floodnet-nyc/flood-sensor/deployment/img/Behind the signs.jpg

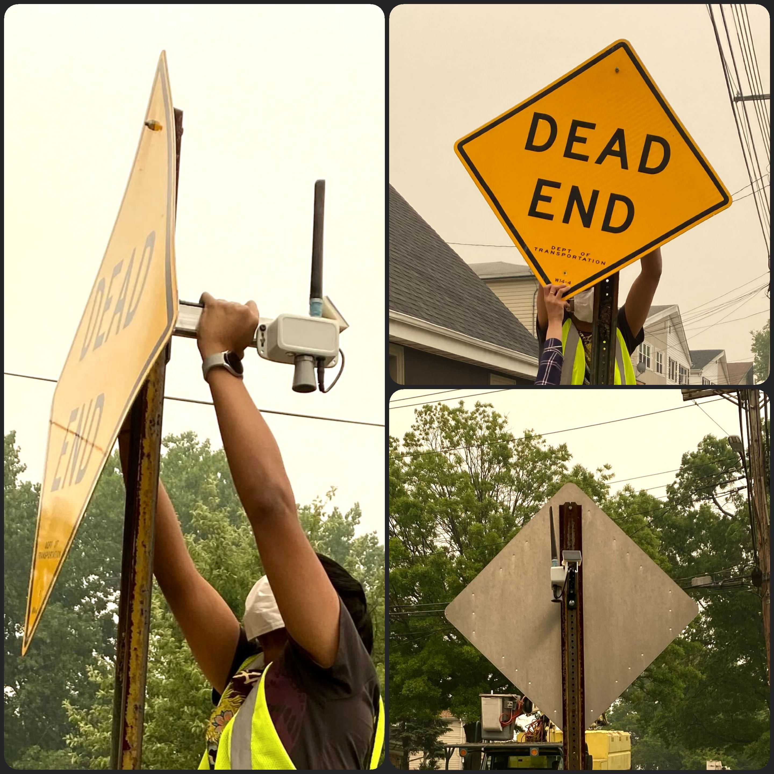
deployment/img/Behind the signs.jpg
