floodnet-nyc/flood-sensor/deployment/img/IMG_3310.jpg

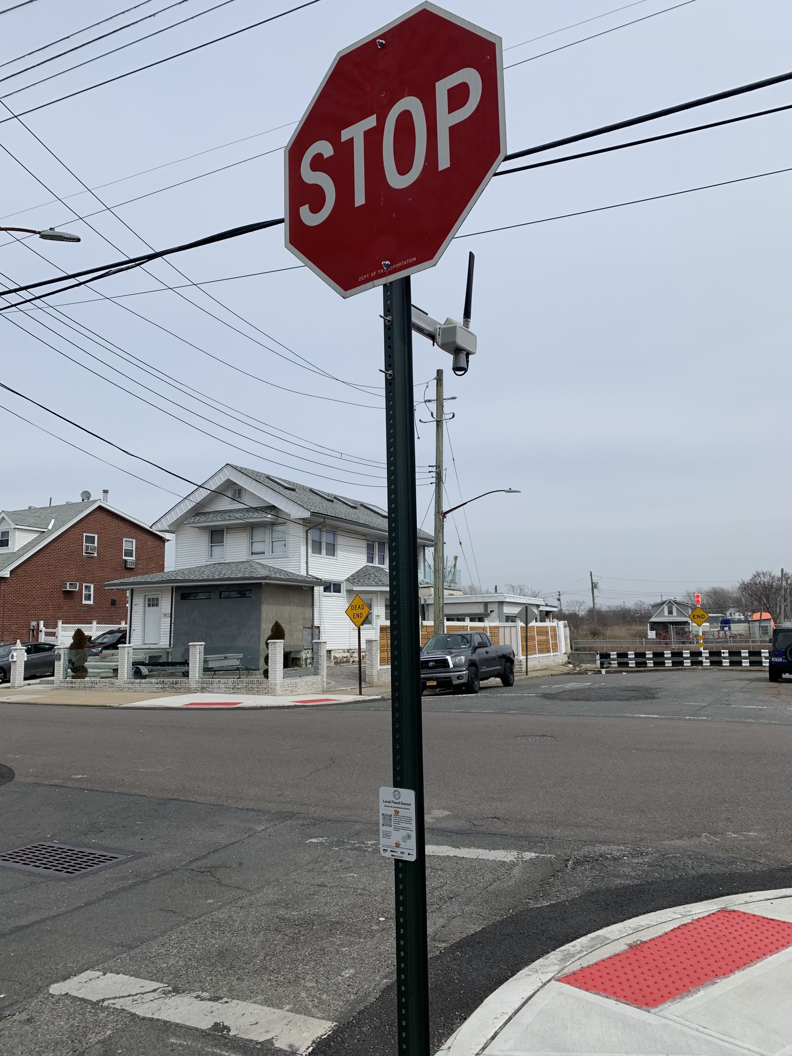
deployment/img/IMG_3310.jpg
