floodnet-nyc/flood-sensor/deployment/img/IMG_3319.jpg

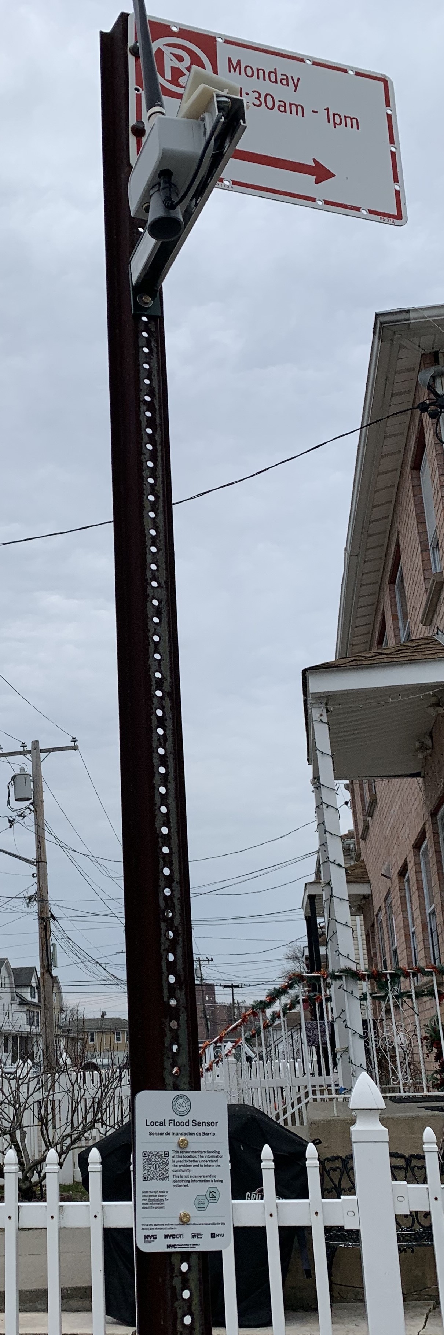
deployment/img/IMG_3319.jpg
