floodnet-nyc/flood-sensor/deployment/img/IMG_3345-1.jpg

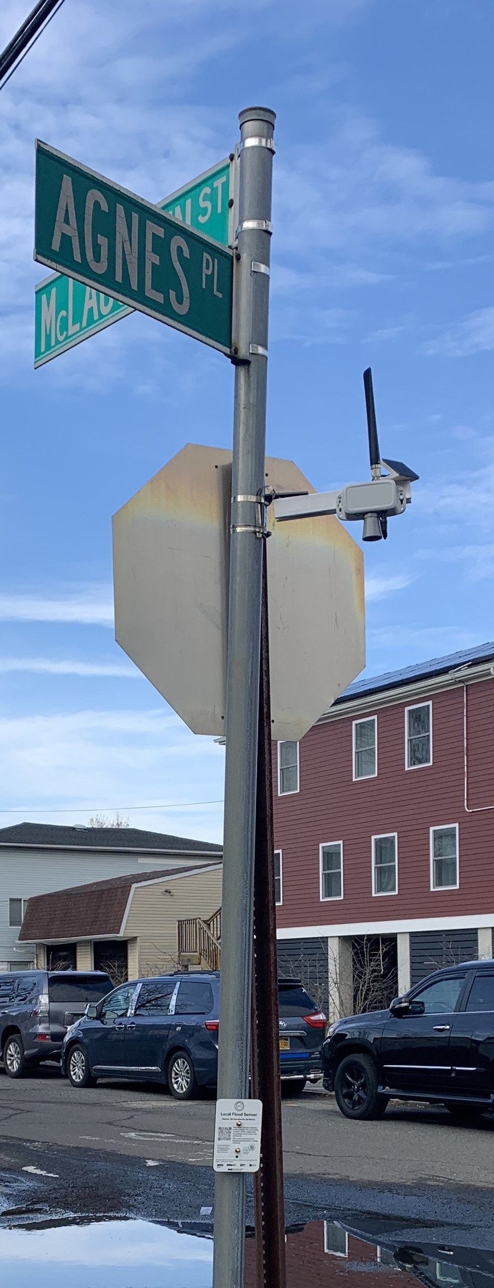
deployment/img/IMG_3345-1.jpg
