floodnet-nyc/flood-sensor/deployment/img/IMG_33191.jpg

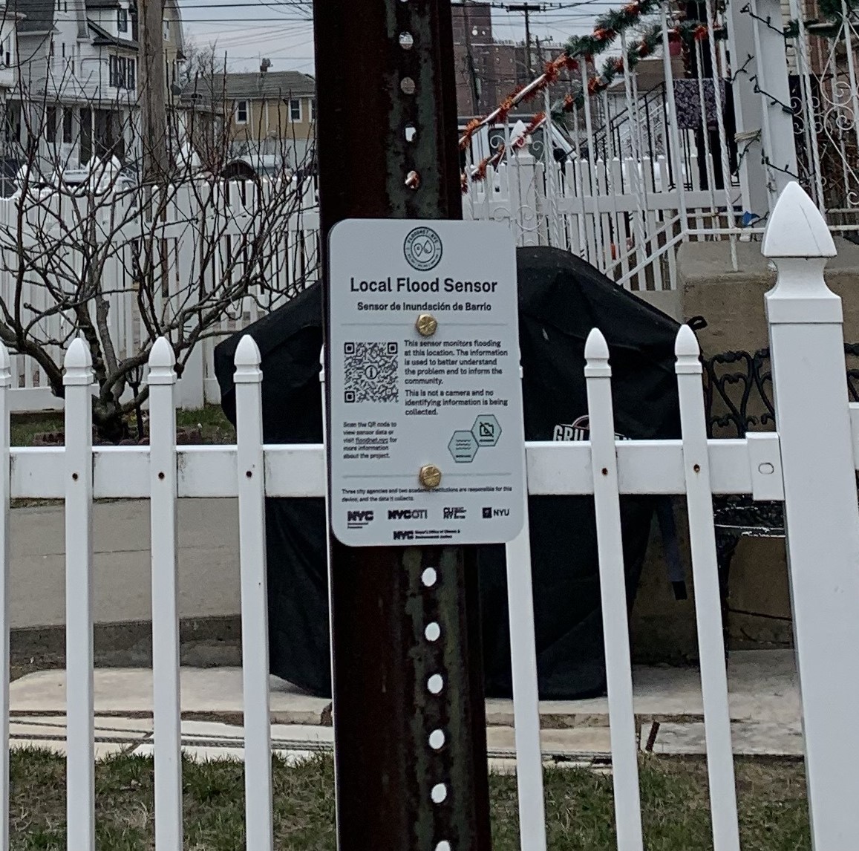
deployment/img/IMG_33191.jpg
