floodnet-nyc/flood-sensor/deployment/img/Sensor on Round pole.jpeg

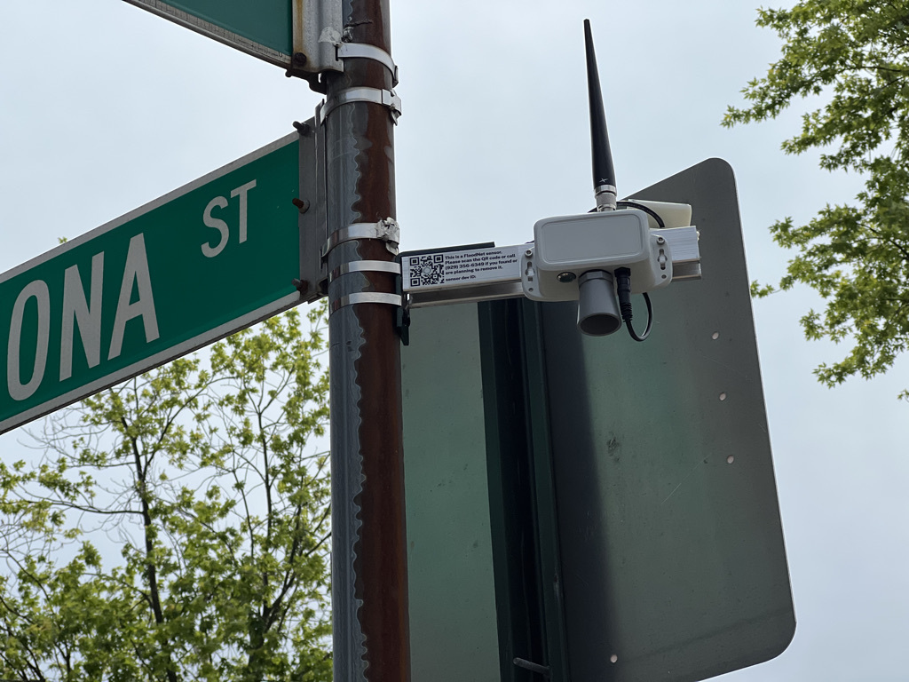
deployment/img/Sensor on Round pole.jpeg
