floodnet-nyc/flood-sensor/img/add-library.png

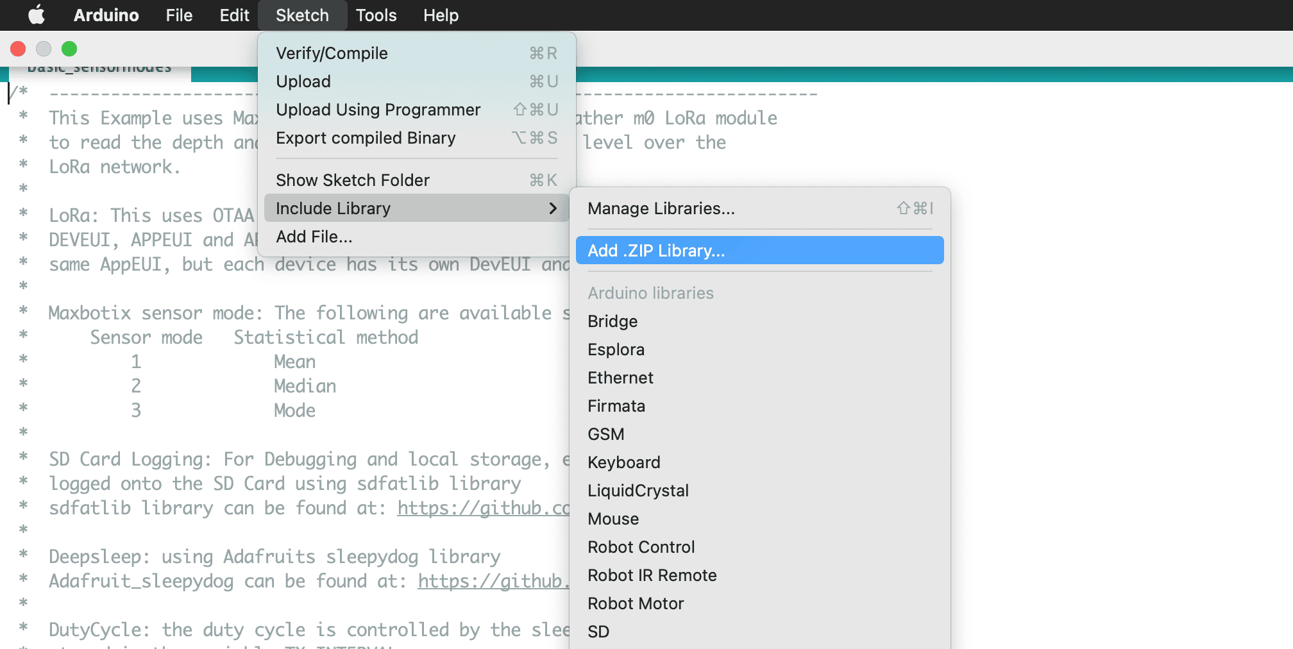
img/add-library.png
