floodnet-nyc/flood-sensor/img/deployment-render.png

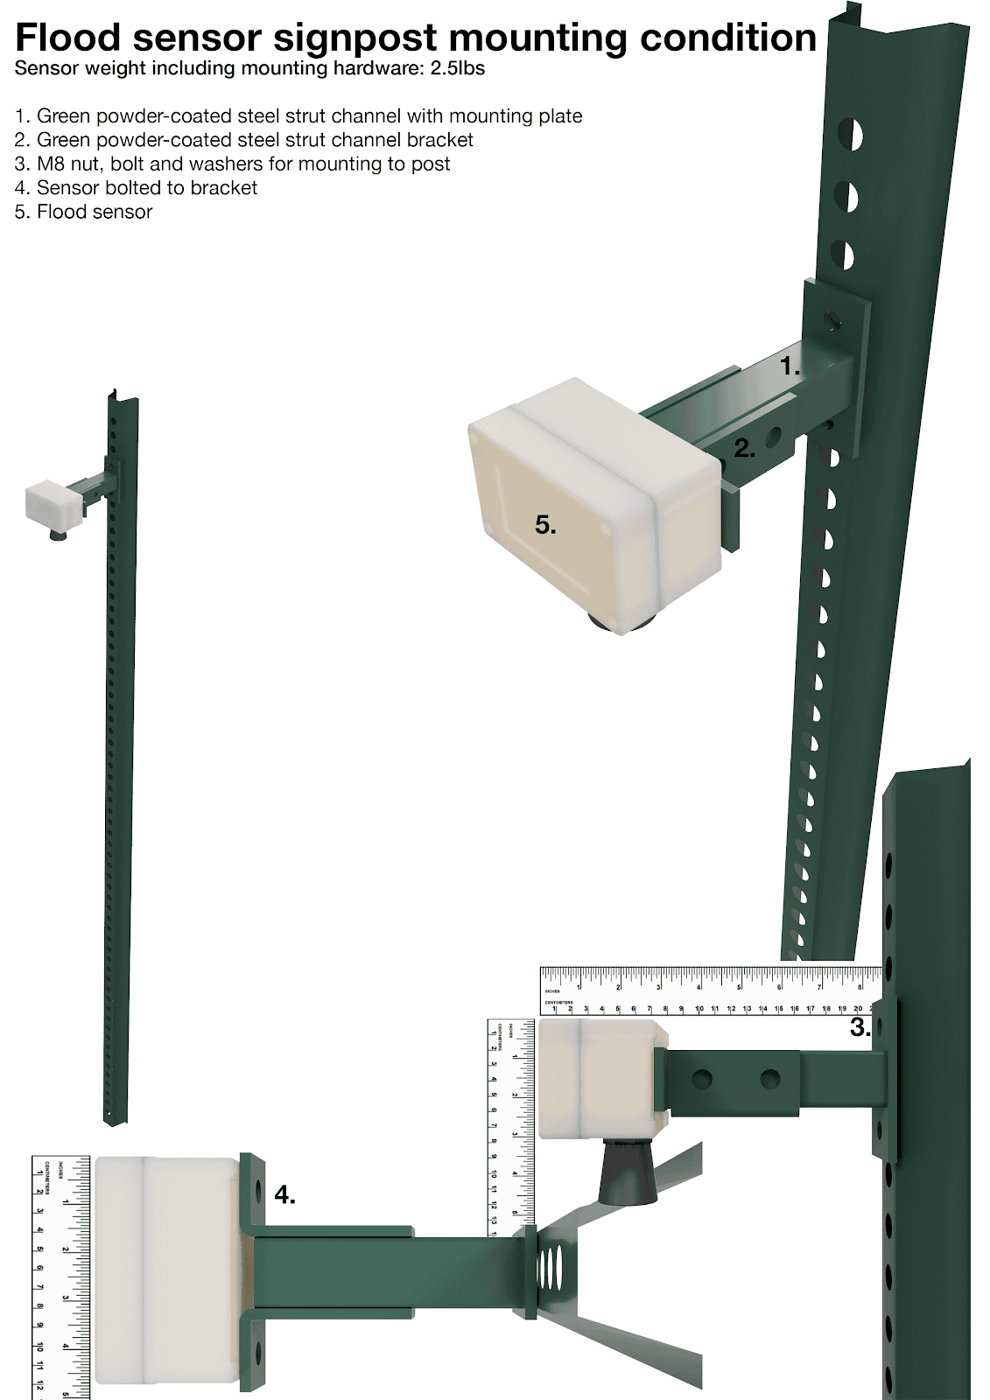
img/deployment-render.png
