floodnet-nyc/flood-sensor/img/design-data-comparison.png

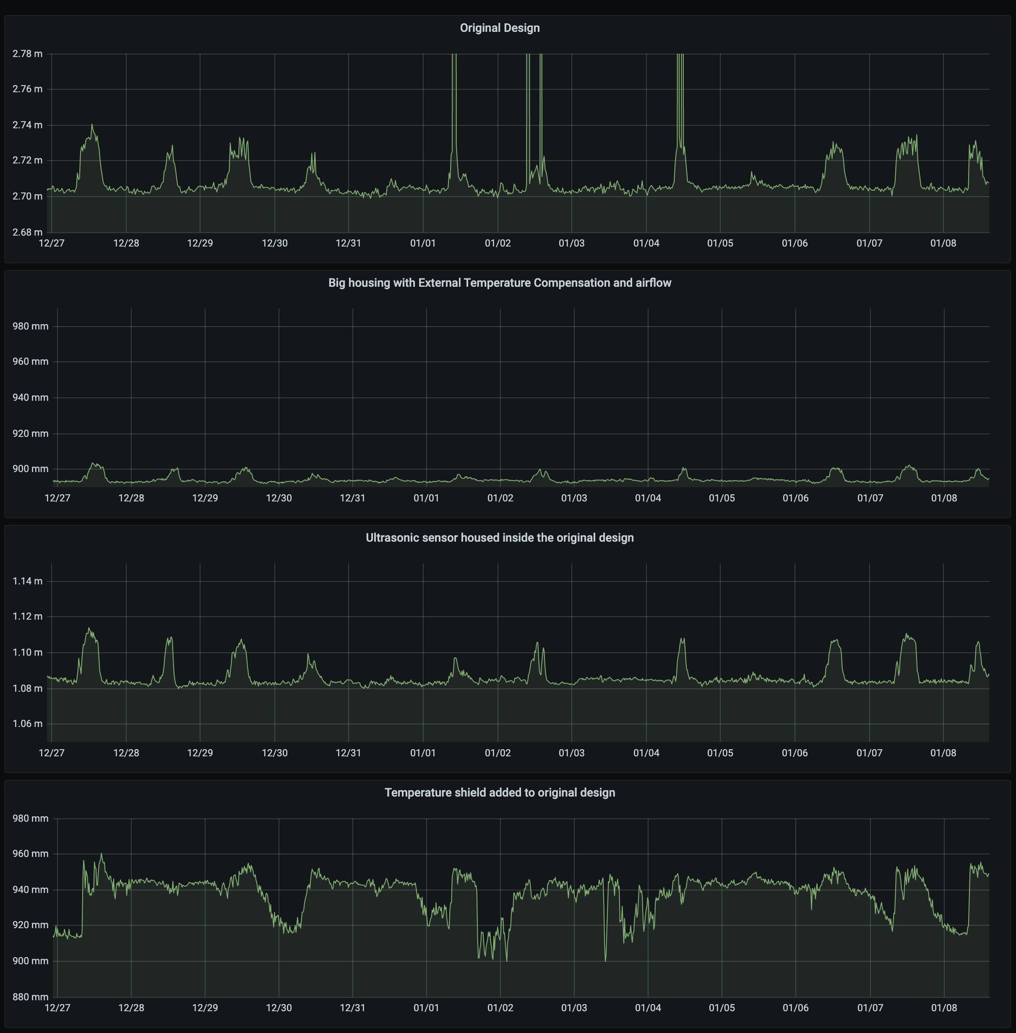
img/design-data-comparison.png
