floodnet-nyc/flood-sensor/img/fritzingcircuit.png

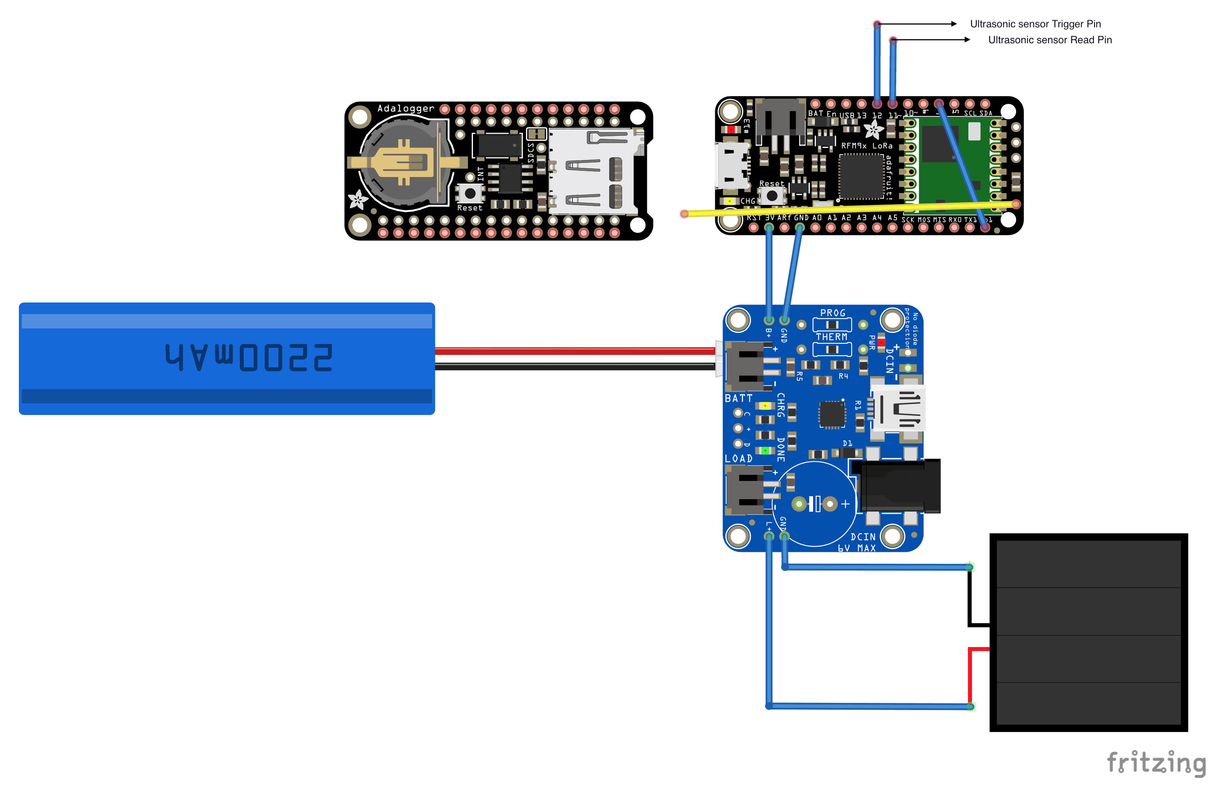
img/fritzingcircuit.png
