floodnet-nyc/flood-sensor/img/front-side-mount-sideview.png

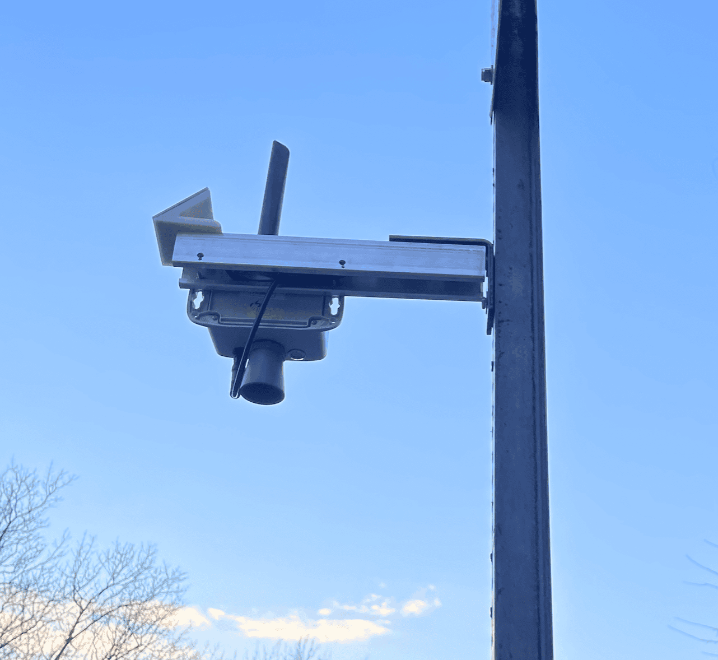
img/front-side-mount-sideview.png
