floodnet-nyc/flood-sensor/img/lora-timing.png

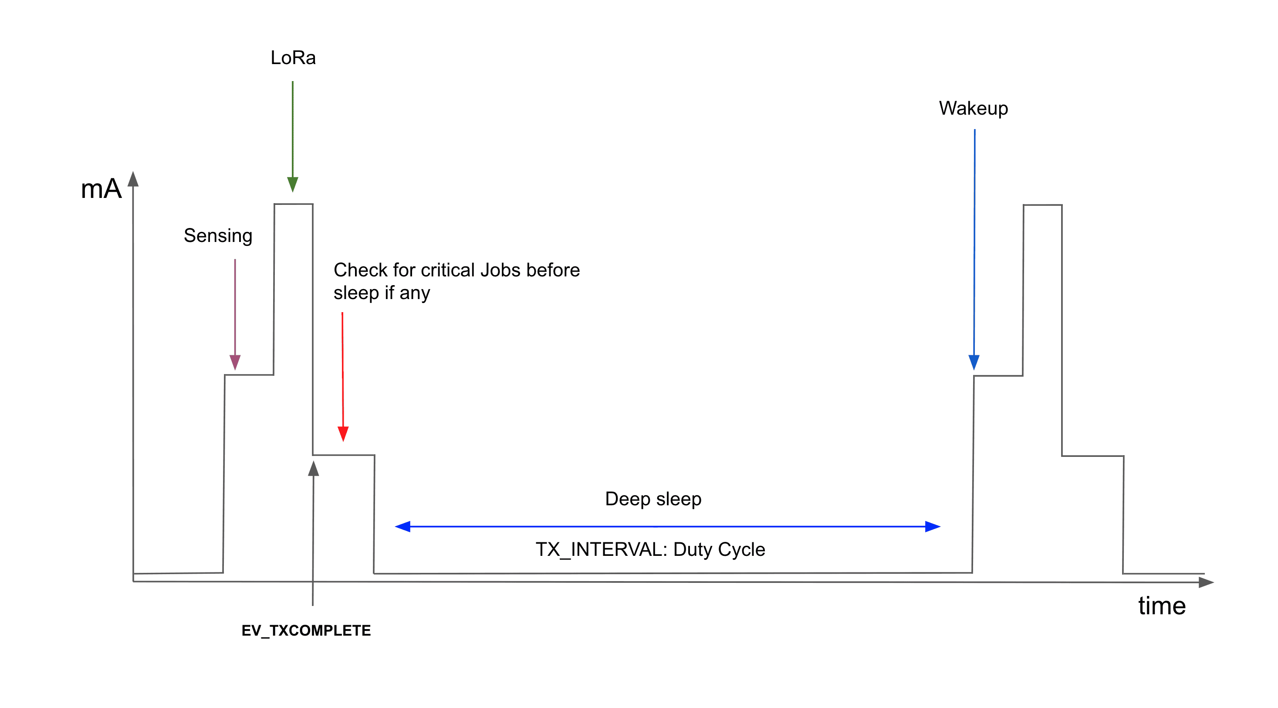
img/lora-timing.png
