floodnet-nyc/flood-sensor/img/low-power-profile.png

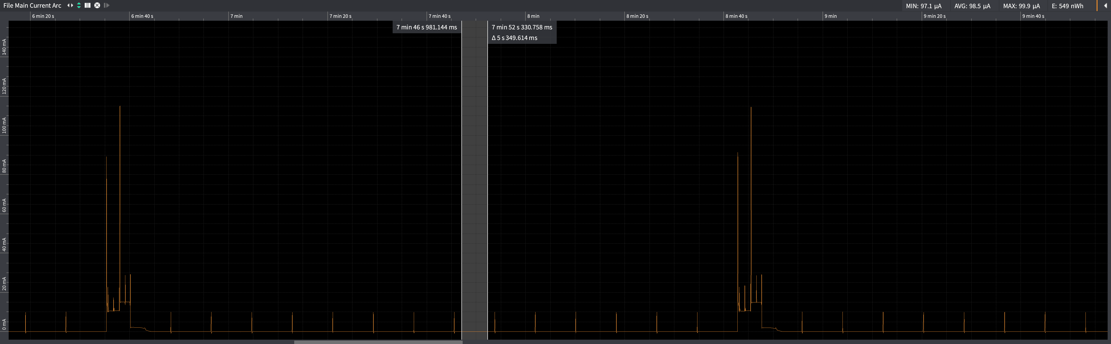
img/low-power-profile.png
