floodnet-nyc/flood-sensor/img/modes_cm.png

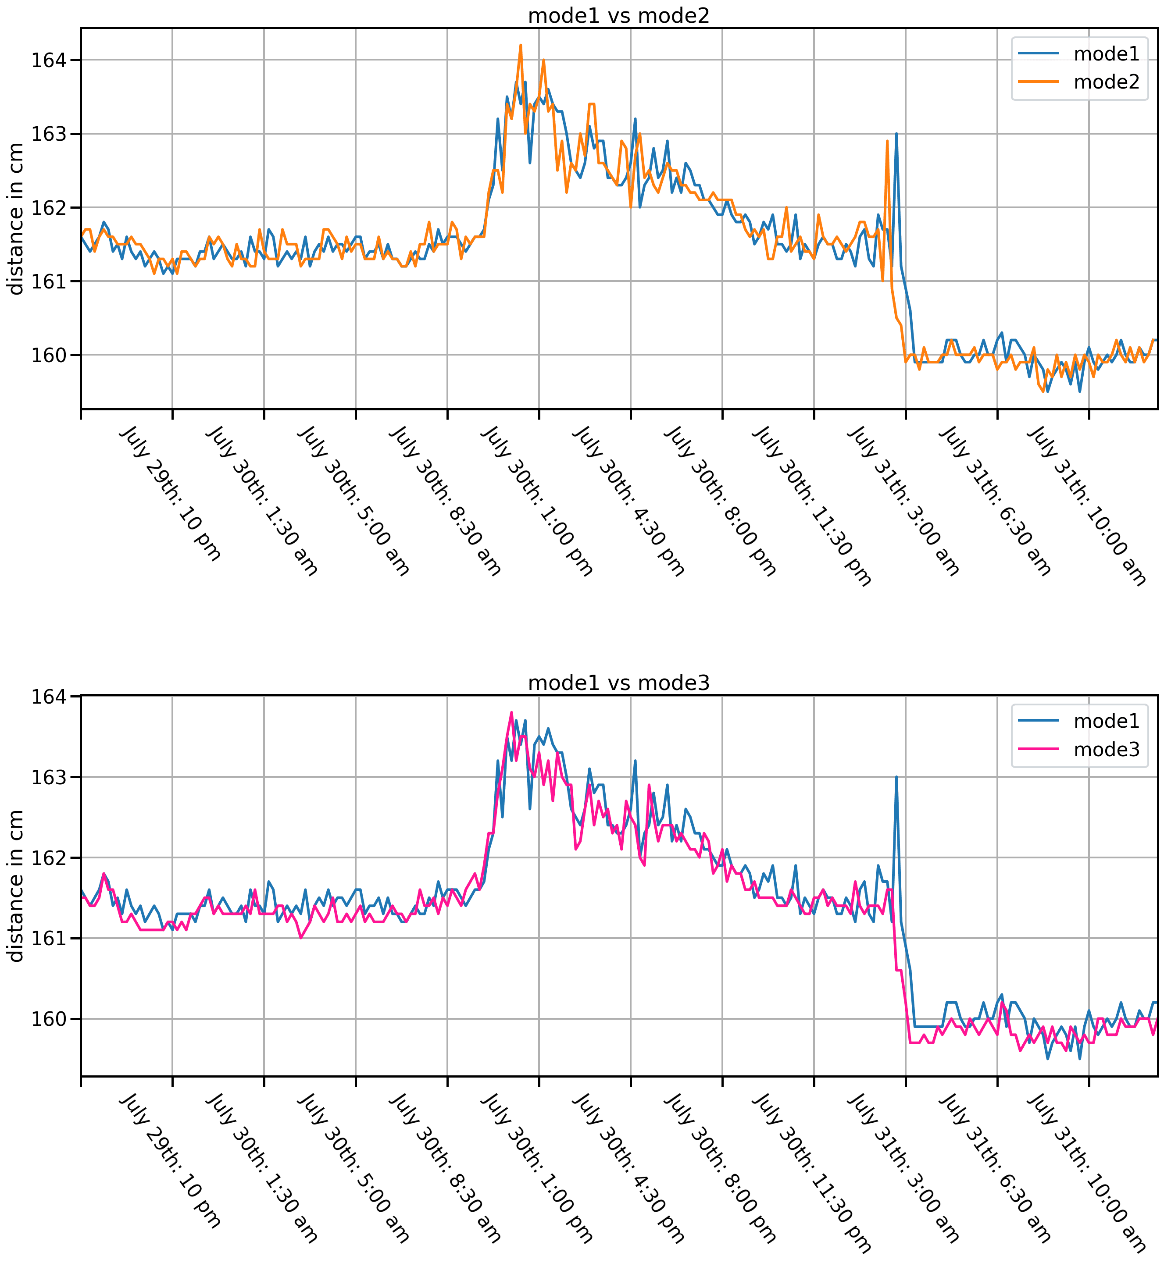
img/modes_cm.png
