floodnet-nyc/flood-sensor/img/mountedv2.jpg

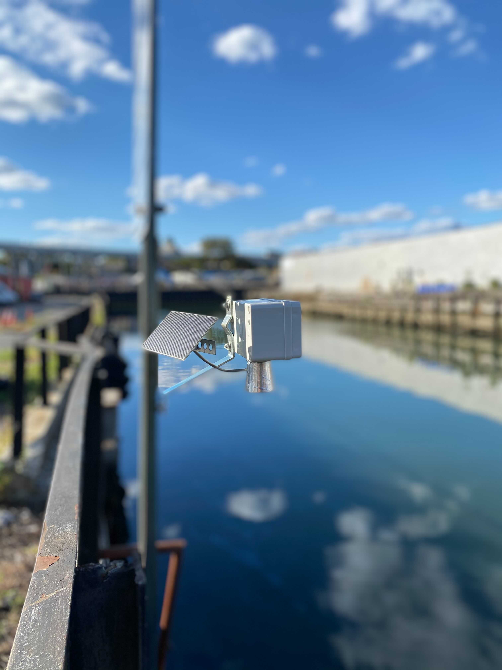
img/mountedv2.jpg
