floodnet-nyc/flood-sensor/img/mounting-seperate-solarboard.jpg

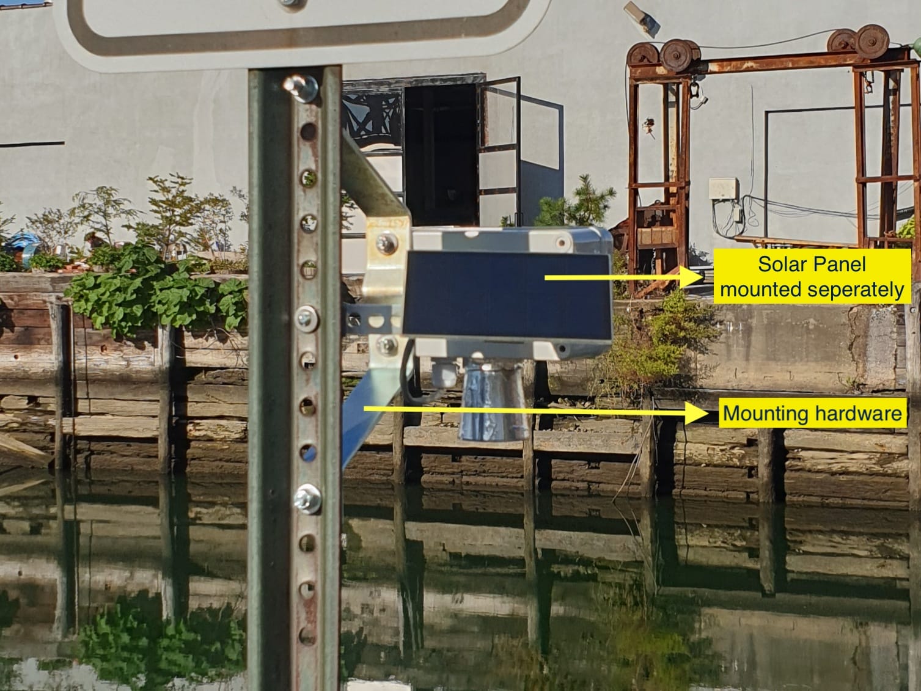
img/mounting-seperate-solarboard.jpg
