floodnet-nyc/flood-sensor/img/sensor-over-sidewalk.jpg

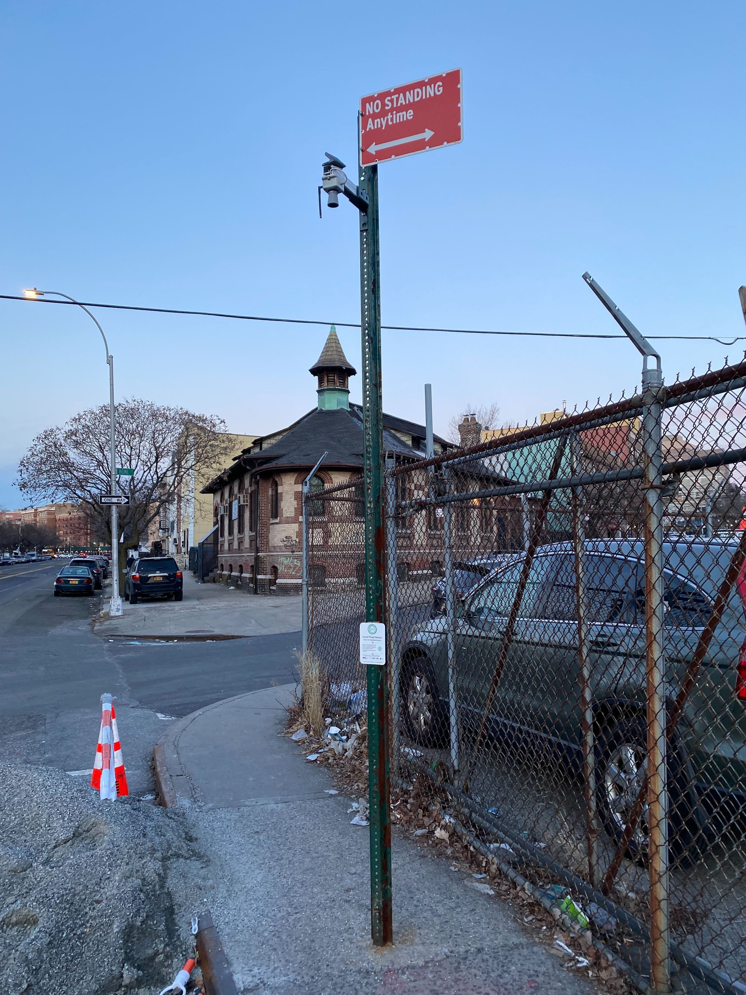
img/sensor-over-sidewalk.jpg
