floodnet-nyc/flood-sensor/img/sensor_states_flow_diagram.png

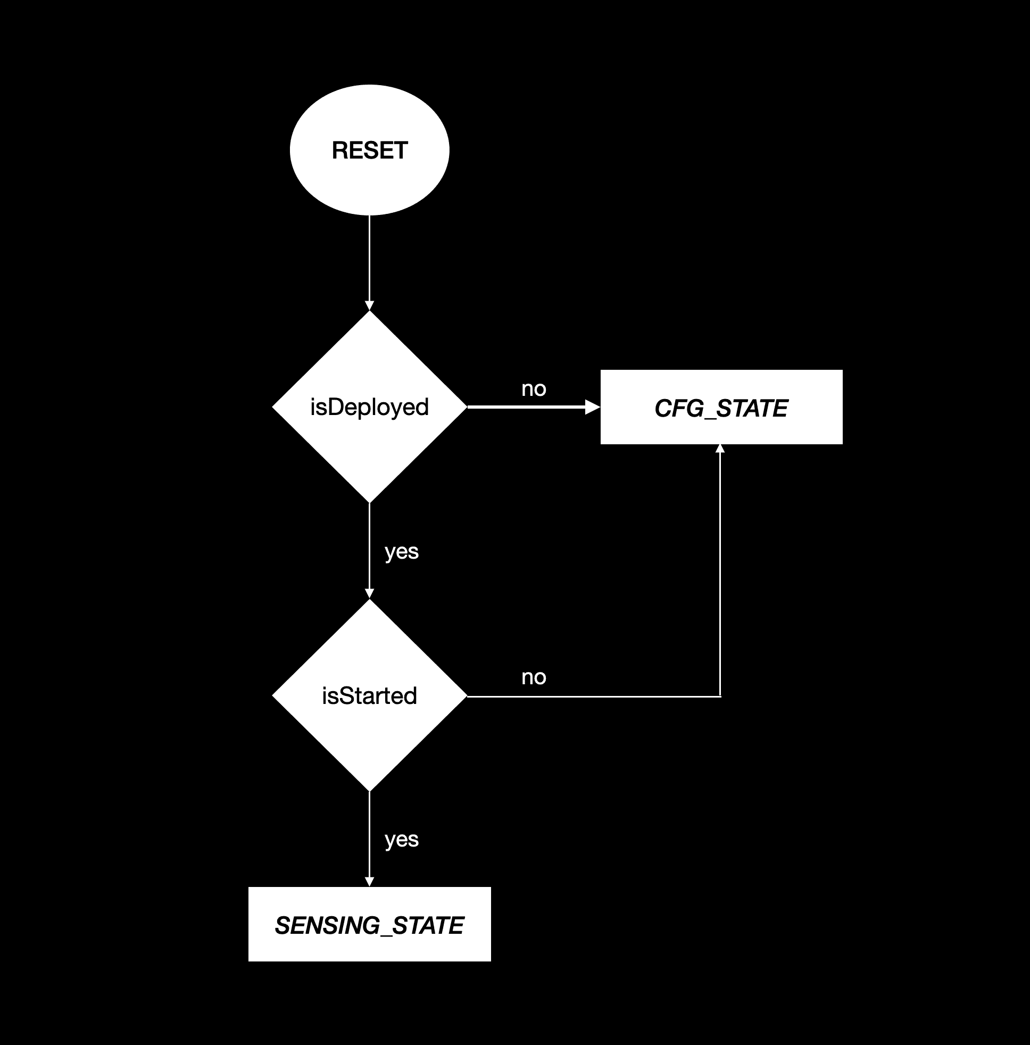
img/sensor_states_flow_diagram.png
