floodnet-nyc/flood-sensor/img/single-core-wireas-antenna.jpg

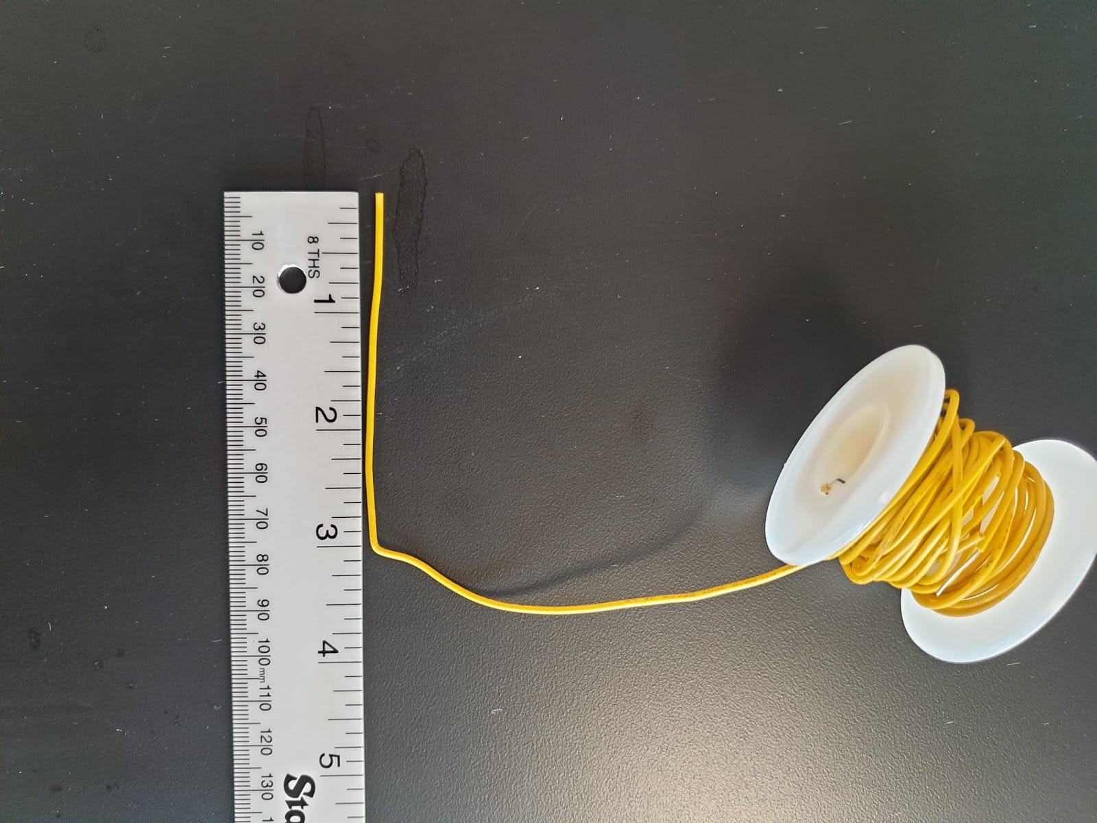
img/single-core-wireas-antenna.jpg
