floodnet-nyc/flood-sensor/img/solar-panel-withboard.jpg

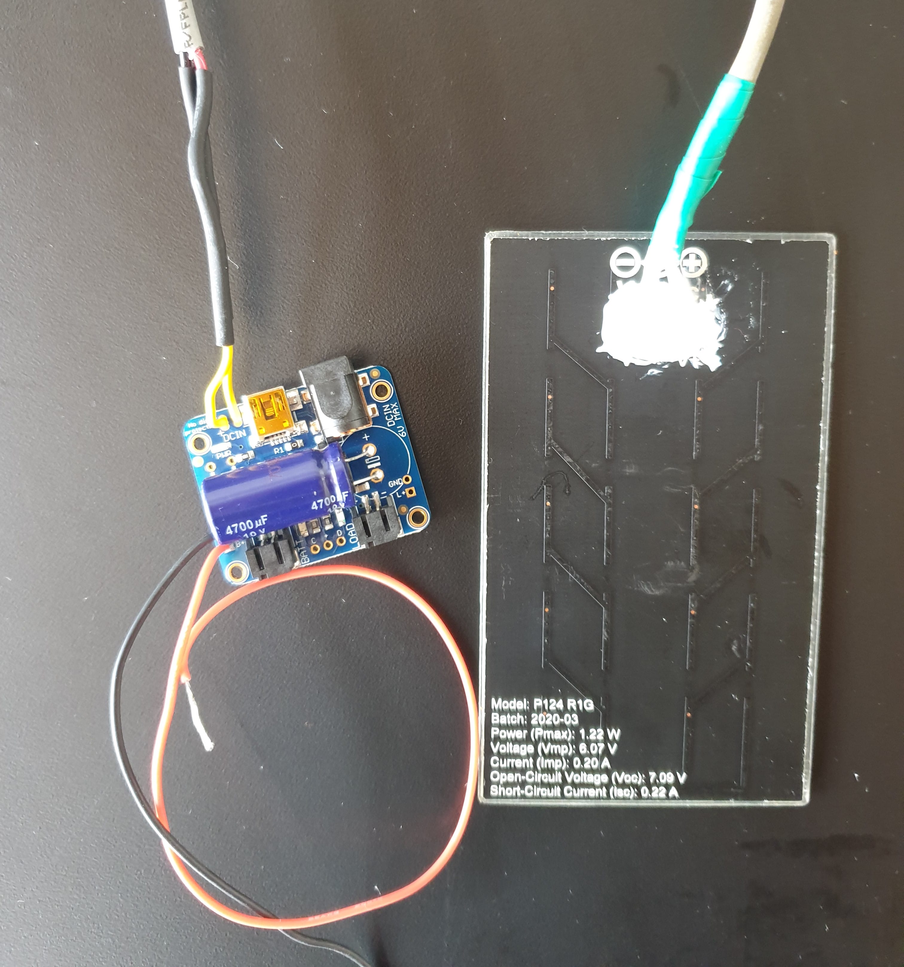
img/solar-panel-withboard.jpg
