floodnet-nyc/flood-sensor/img/street-mounting.png

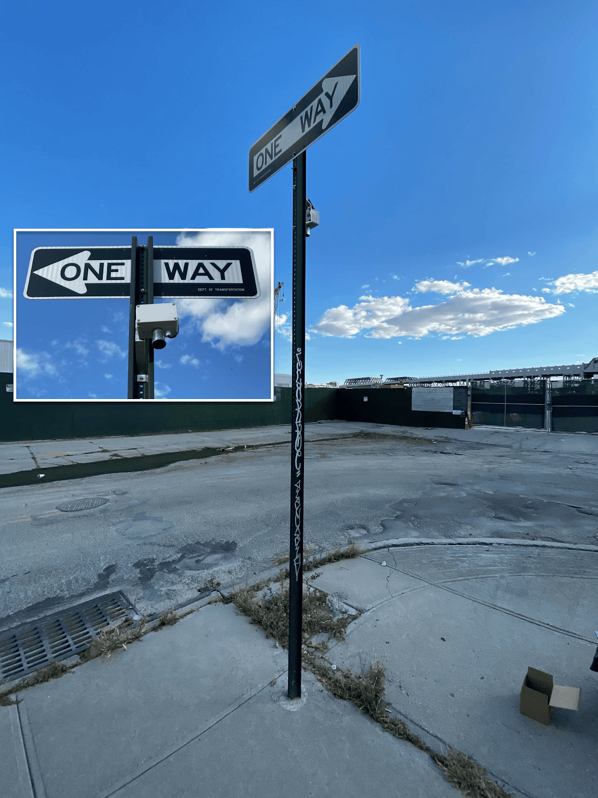
img/street-mounting.png
