floodnet-nyc/flood-sensor/img/Streetsignmount.jpg

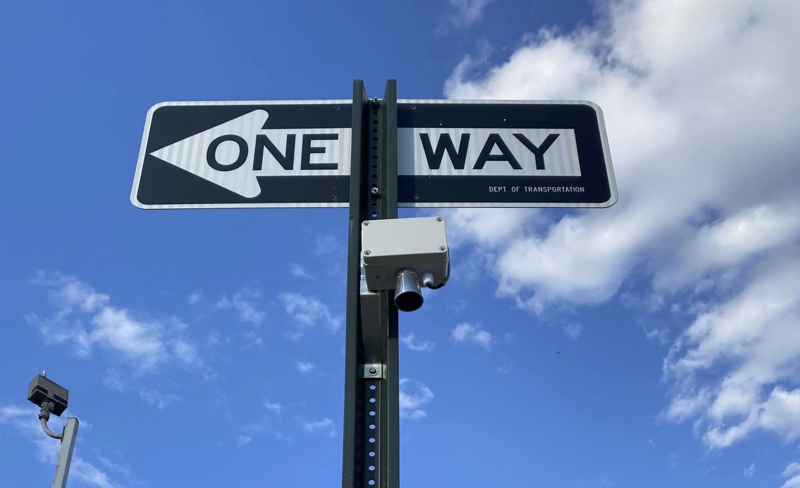
img/Streetsignmount.jpg
