floodnet-nyc/flood-sensor/img/ultrasonic-sensor-inside.jpg

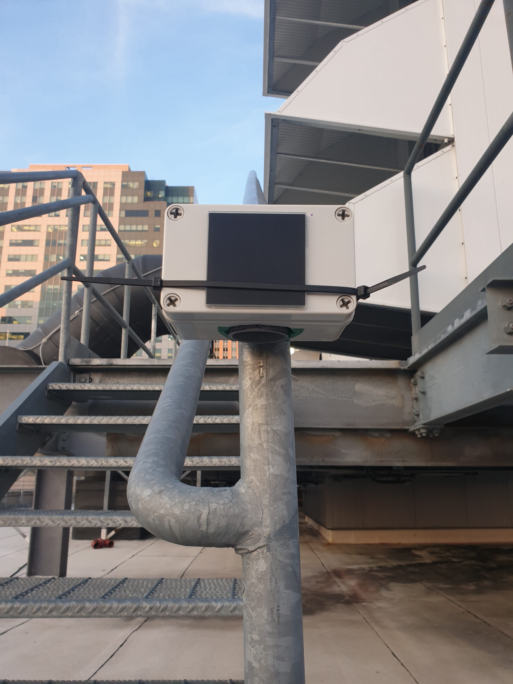
img/ultrasonic-sensor-inside.jpg
