floodnet-nyc/flood-sensor/img/UltrasonicvsTemp_aug22nd_.png

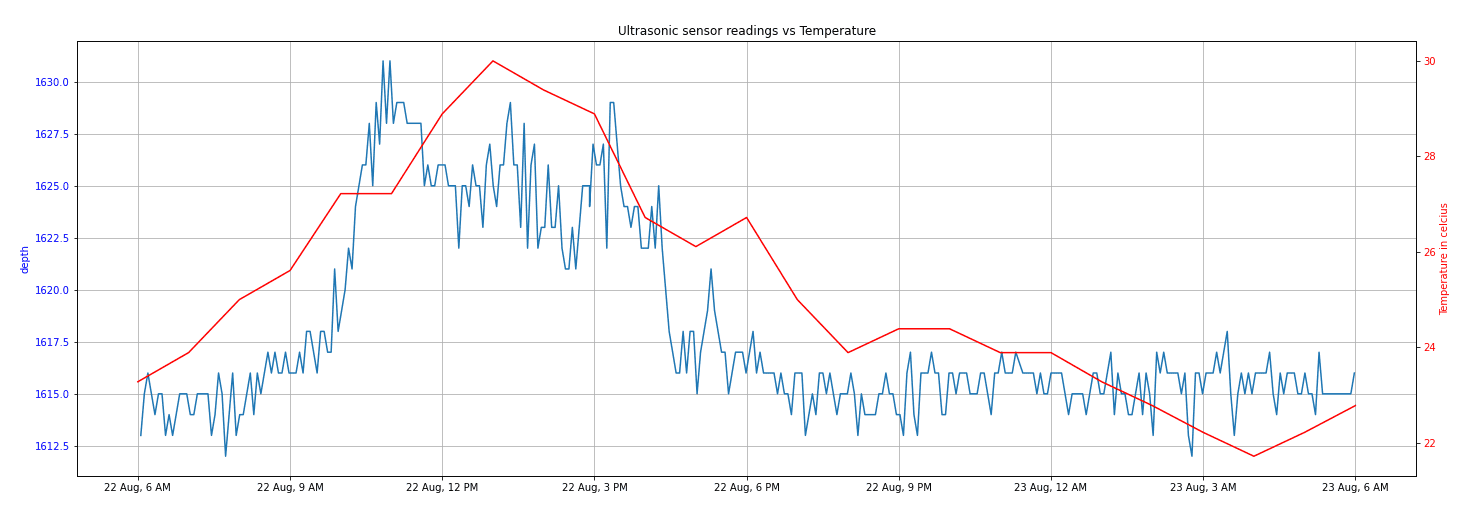
img/UltrasonicvsTemp_aug22nd_.png
