floodnet-nyc/flood-sensor/img/using-larger-housing.jpg

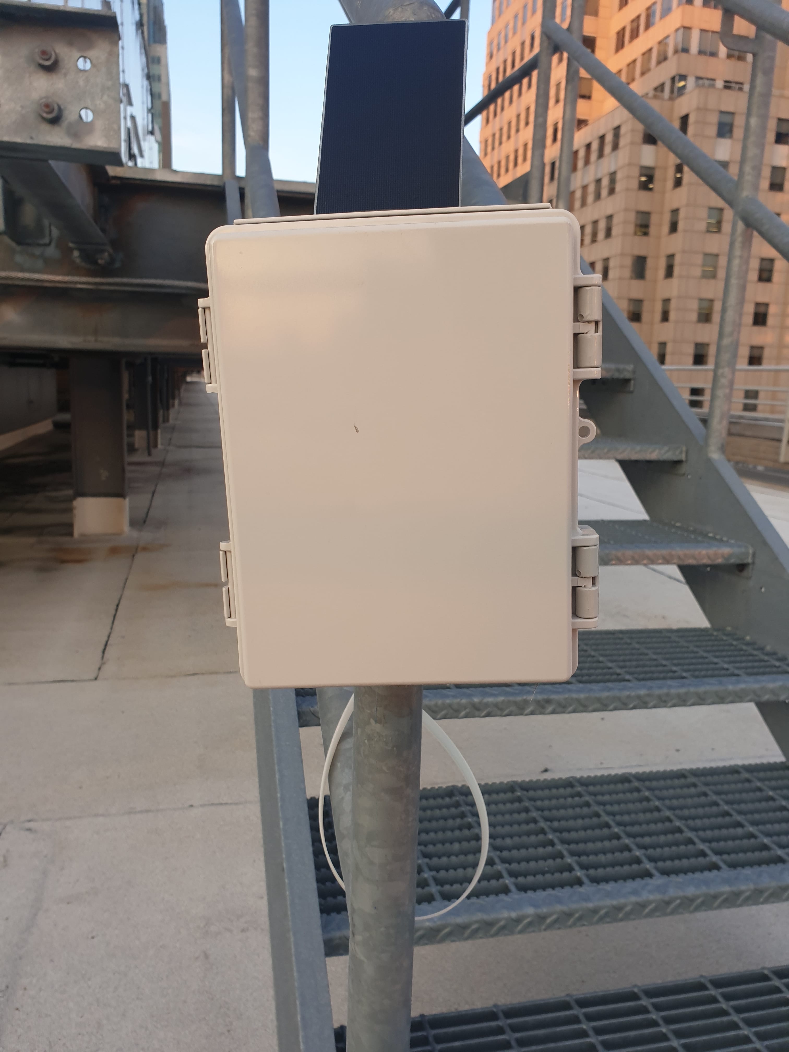
img/using-larger-housing.jpg
