floodnet-nyc/flood-sensor/img/assembled-mcu.jpg

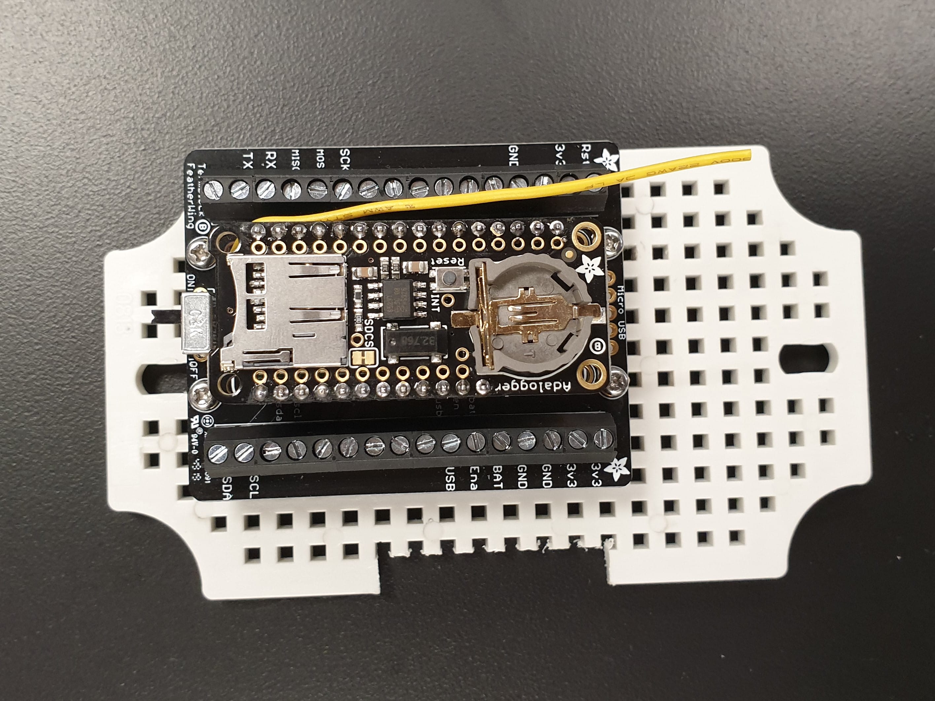
img/assembled-mcu.jpg
