floodnet-nyc/flood-sensor/firmware/functions.h

#ifndef FUNCTIONS_H
#define FUNCTIONS_H

#include <Arduino.h>

void printHex2(unsigned v);
void swap(uint16_t  *p, uint16_t  *q);
void sort(uint16_t a[], size_t n);
uint16_t mean(uint16_t readings_arr[], size_t n, unsigned int sensor_numberOfReadings);
uint16_t median(uint16_t readings_arr[], size_t n, unsigned int sensor_numberOfReadings);
uint16_t mode(uint16_t readings_arr[], size_t n, unsigned int sensor_numberOfReadings);

#endif
